PaulZC/NEO-M8T_GNSS_FeatherWing/img/PCB_BOTTOM.jpg

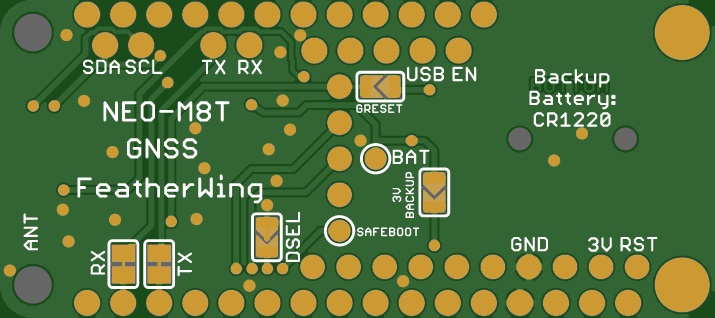
img/PCB_BOTTOM.jpg
