PaulZC/NEO-M8T_GNSS_FeatherWing/img/PCB_TOP.jpg

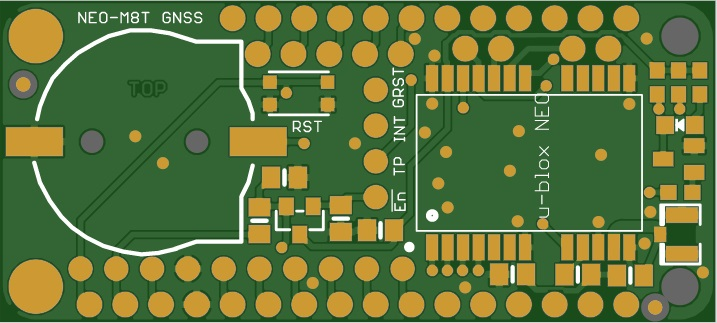
img/PCB_TOP.jpg
