PaulZC/NEO-M8T_GNSS_FeatherWing/Python/NEO-M8T_GNSS_RAWX_Logger.py

## U-Blox NEO-M8T GNSS RAWX Logger

## Hardware:
## Paul's NEO-M8T GNSS FeatherWing:
## https://github.com/PaulZC/NEO-M8T_GNSS_FeatherWing
## Mounted on the Adafruit Feather M0 Adalogger:
## https://www.adafruit.com/product/2796
## https://learn.adafruit.com/adafruit-feather-m0-adalogger

## Assumes that the Adalogger is running UBX_Echo
## https://github.com/PaulZC/NEO-M8T_GNSS_FeatherWing/tree/master/Arduino/UBX_Echo

## Logs RXM-RAWX, RXM-SFRBX and TIM-TM2 messages to file

import serial
import time
import sys
import signal
import logging

# https://stackoverflow.com/questions/842557/how-to-prevent-a-block-of-code-from-being-interrupted-by-keyboardinterrupt-in-py
class DelayedKeyboardInterrupt(object):
    def __enter__(self):
        self.signal_received = False
        self.old_handler = signal.getsignal(signal.SIGINT)
        signal.signal(signal.SIGINT, self.handler)

    def handler(self, sig, frame):
        self.signal_received = (sig, frame)
        logging.debug('SIGINT received. Delaying KeyboardInterrupt.')

    def __exit__(self, type, value, traceback):
        signal.signal(signal.SIGINT, self.old_handler)
        if self.signal_received:
            self.old_handler(*self.signal_received)

class UBXport(object):

    def __init__(self,baud=115200):
        ''' Init UBXport - open the serial port '''
        com_port = raw_input('Which serial port do you want to use (default COM1)? ')
        if com_port == '': com_port = 'COM1'

        # Open port
        try:
            self.ser1 = serial.Serial(com_port, baud, timeout=0.1)
        except:
            raise NameError('COULD NOT OPEN SERIAL PORT!')

        self.ser1.flushInput()

    def sendNMEA(self,msg,wait=10,biglen=200):
        ''' Send a message in NMEA format (adding $ and *, the checksum, and \r\n) and wait for a reply '''
        a = []
        a += "$" + msg + "*"
        csum = 0 
        for c in a[1:-1]: csum ^= ord(c)        
        a += "%02X"%csum + '\r\n'
        print 'Sending:'
        print ''.join(a[:-2])
        for c in a: self.ser1.write(c)
        if wait > 0:
            print 'Received:'
            for x in range(wait):
                RX = up.ser1.read(biglen)
                if RX != '': sys.stdout.write(RX)

    def sendUBX(self,msg,wait=10,biglen=200):
        ''' Send a message in UBX format (adding the checksum) and wait for a reply '''
        a = []
        a += msg
        sum1 = 0
        sum2 = 0
        for c in a[2:]:
            sum1 = sum1 + ord(c)
            sum2 = sum2 + sum1
        a += chr(sum1&0xFF)
        a += chr(sum2&0xFF)
        print 'Sending:'
        print "\\x" + "\\x".join("{:02x}".format(ord(c)) for c in a)
        for c in a: self.ser1.write(c)
        if wait > 0:
            print 'Received:'
            for x in range(wait):
                RX = self.ser1.read(biglen)
                if RX != '':
                    print "\\x" + "\\x".join("{:02x}".format(ord(c)) for c in RX)

rx = ''
    
try:
    print 'NEO-M8T GNSS RAWX Logger'
    print
    
    up = UBXport() # Open port

    # Disable all default NMEA messages
    print 'Disabling GLL'
    up.sendNMEA("PUBX,40,GLL,0,0,0,0")
    print 'Disabling ZDA'
    up.sendNMEA("PUBX,40,ZDA,0,0,0,0")
    print 'Disabling VTG'
    up.sendNMEA("PUBX,40,VTG,0,0,0,0")
    print 'Disabling GSV'
    up.sendNMEA("PUBX,40,GSV,0,0,0,0")
    print 'Disabling GSA'
    up.sendNMEA("PUBX,40,GSA,0,0,0,0")
    print 'Disabling RMC'
    up.sendNMEA("PUBX,40,RMC,0,0,0,0")       
    print 'Disabling GGA'
    up.sendNMEA("PUBX,40,GGA,0,0,0,0")       

    # Set Navigation Mode
    print
    print 'Setting Nav Mode'
    print '\\xb5\\x62\\x05\\x01... indicates ACK'
    print '\\xb5\\x62\\x05\\x00... indicates NACK'
    # Get Navigation Engine
    #up.sendUBX("\xB5\x62\x06\x24\x00\x00")
    # Default:   \xb5\x62\x06\x24\x24\x00\xff\xff\x02\x03\x00\x00\x00\x00\x10\x27\x00\x00\x05\x00\xfa\x00\xfa\x00\x64\x00\x5e\x01\x00\x3c\x00\x00\x00\x00\x00\x00\x03\x00\x00\x00\x00\x00
    # Set Navigation Engine dynModel to "Stationary"
    # Set tAcc to 350
    # Set dgnssTimeout to zero
    # Set utcStandard to UTC
    up.sendUBX("\xB5\x62\x06\x24\x24\x00\xFF\xFF\x02\x03\x00\x00\x00\x00\x10\x27\x00\x00\x05\x00\xFA\x00\xFA\x00\x64\x00\x5e\x01\x00\x00\x00\x00\x00\x00\x00\x00\x03\x00\x00\x00\x00\x00")
    # Set Navigation Engine dynModel to "Portable"
    #up.sendUBX("\xB5\x62\x06\x24\x24\x00\xFF\xFF\x00\x03\x00\x00\x00\x00\x10\x27\x00\x00\x05\x00\xFA\x00\xFA\x00\x64\x00\x5e\x01\x00\x00\x00\x00\x00\x00\x00\x00\x03\x00\x00\x00\x00\x00")
    # Set Navigation Engine dynModel to "Pedestrian"
    #up.sendUBX("\xB5\x62\x06\x24\x24\x00\xFF\xFF\x03\x03\x00\x00\x00\x00\x10\x27\x00\x00\x05\x00\xFA\x00\xFA\x00\x64\x00\x5e\x01\x00\x00\x00\x00\x00\x00\x00\x00\x03\x00\x00\x00\x00\x00")
    # Set Navigation Engine dynModel to "Automotive"
    #up.sendUBX("\xB5\x62\x06\x24\x24\x00\xFF\xFF\x04\x03\x00\x00\x00\x00\x10\x27\x00\x00\x05\x00\xFA\x00\xFA\x00\x64\x00\x5e\x01\x00\x00\x00\x00\x00\x00\x00\x00\x03\x00\x00\x00\x00\x00")
    # Set Navigation Engine dynModel to "Sea"
    #up.sendUBX("\xB5\x62\x06\x24\x24\x00\xFF\xFF\x05\x03\x00\x00\x00\x00\x10\x27\x00\x00\x05\x00\xFA\x00\xFA\x00\x64\x00\x5e\x01\x00\x00\x00\x00\x00\x00\x00\x00\x03\x00\x00\x00\x00\x00")
    # Set Navigation Engine dynModel to "Airborne <1G"
    #up.sendUBX("\xB5\x62\x06\x24\x24\x00\xFF\xFF\x06\x03\x00\x00\x00\x00\x10\x27\x00\x00\x05\x00\xFA\x00\xFA\x00\x64\x00\x5e\x01\x00\x00\x00\x00\x00\x00\x00\x00\x03\x00\x00\x00\x00\x00")

    # Config NMEA Talker ID
    print
    print 'Setting NMEA Config'
    # Get NMEA
    #up.sendUBX("\xb5\x62\x06\x17\x00\x00")
    # Default:   \xb5\x62\x06\x17\x14\x00\x00\x40\x00\x02\x00\x00\x00\x00\x00\x00\x00\x01\x00\x00\x00\x00\x00\x00\x00\x00
    # Set NMEA Config:
    # Set trackFilt to 1 to ensure course (COG) is always output
    # Set Main Talker ID to 'GP' to avoid having to modify TinyGPS
    up.sendUBX("\xb5\x62\x06\x17\x14\x00\x20\x40\x00\x02\x00\x00\x00\x00\x00\x01\x01\x01\x00\x00\x00\x00\x00\x00\x00\x00")
    # Set Main Talker ID to 'GN'
    #up.sendUBX("\xb5\x62\x06\x17\x14\x00\x20\x40\x00\x02\x00\x00\x00\x00\x00\x03\x01\x01\x00\x00\x00\x00\x00\x00\x00\x00")

    # Configure GNSS
    print
    print 'Configuring GNSS'
    # Get GNSS
    #up.sendUBX("\xb5\x62\x06\x3e\x00\x00")
    # Default:   \xb5\x62\x06\x3e\x3c\x00\x00\x20\x20\x07\x00\x08\x10\x00\x01\x00\x01\x01\x01\x01\x03\x00\x00\x00\x01\x01\x02\x04\x08\x00\x00\x00\x01\x01\x03\x08\x10\x00\x00\x00\x01\x01\x04\x00\x08\x00\x00\x00\x01\x03\x05\x00\x03\x00\x01\x00\x01\x05\x06\x08\x0e\x00\x01\x00\x01\x01
    # Set GNSS: GPS + QZSS + GLONASS (Default on NEO-M8T)
    #up.sendUBX("\xb5\x62\x06\x3e\x3c\x00\x00\x20\x20\x07\x00\x08\x10\x00\x01\x00\x01\x01\x01\x01\x03\x00\x00\x00\x01\x01\x02\x04\x08\x00\x00\x00\x01\x01\x03\x08\x10\x00\x00\x00\x01\x01\x04\x00\x08\x00\x00\x00\x01\x03\x05\x00\x03\x00\x01\x00\x01\x05\x06\x08\x0e\x00\x01\x00\x01\x01",30)
    # Set GNSS: GPS + Galileo + GLONASS
    #up.sendUBX("\xb5\x62\x06\x3e\x3c\x00\x00\x20\x20\x07\x00\x08\x10\x00\x01\x00\x01\x01\x01\x01\x03\x00\x00\x00\x01\x01\x02\x04\x08\x00\x01\x00\x01\x01\x03\x08\x10\x00\x00\x00\x01\x01\x04\x00\x08\x00\x00\x00\x01\x03\x05\x00\x03\x00\x00\x00\x01\x05\x06\x08\x0e\x00\x01\x00\x01\x01",30)
    # Set GNSS: GPS + Galileo + BeiDou
    #up.sendUBX("\xb5\x62\x06\x3e\x3c\x00\x00\x20\x20\x07\x00\x08\x10\x00\x01\x00\x01\x01\x01\x01\x03\x00\x00\x00\x01\x01\x02\x04\x08\x00\x01\x00\x01\x01\x03\x08\x10\x00\x01\x00\x01\x01\x04\x00\x08\x00\x00\x00\x01\x03\x05\x00\x03\x00\x00\x00\x01\x05\x06\x08\x0e\x00\x00\x00\x01\x01",30)
    # Set GNSS: GPS + Galileo + GLONASS + SBAS
    up.sendUBX("\xb5\x62\x06\x3e\x3c\x00\x00\x20\x20\x07\x00\x08\x10\x00\x01\x00\x01\x01\x01\x01\x03\x00\x01\x00\x01\x01\x02\x04\x08\x00\x01\x00\x01\x01\x03\x08\x10\x00\x00\x00\x01\x01\x04\x00\x08\x00\x00\x00\x01\x03\x05\x00\x03\x00\x00\x00\x01\x05\x06\x08\x0e\x00\x01\x00\x01\x01",30)
    # Set GNSS: GPS + Galileo + BeiDou + SBAS
    #up.sendUBX("\xb5\x62\x06\x3e\x3c\x00\x00\x20\x20\x07\x00\x08\x10\x00\x01\x00\x01\x01\x01\x01\x03\x00\x01\x00\x01\x01\x02\x04\x08\x00\x01\x00\x01\x01\x03\x08\x10\x00\x01\x00\x01\x01\x04\x00\x08\x00\x00\x00\x01\x03\x05\x00\x03\x00\x00\x00\x01\x05\x06\x08\x0e\x00\x00\x00\x01\x01",30)

    # Change Navigation/Measurement Rate
    print
    print 'Setting Measurement Rate'
    # Get CFG-RATE
    #up.sendUBX("\xb5\x62\x06\x08\x00\x00")
    # Default:   \xb5\x62\x06\x08\x06\x00\xe8\x03\x01\x00\x01\x00
    # Set CFG-RATE: set measRate to 250msec; align to UTC time
    up.sendUBX("\xb5\x62\x06\x08\x06\x00\xfa\x00\x01\x00\x00\x00")
    # Set CFG-RATE: set measRate to 250msec; align to GPS time
    #up.sendUBX("\xb5\x62\x06\x08\x06\x00\xfa\x00\x01\x00\x01\x00")
    # Set CFG-RATE: set measRate to 500msec; align to UTC time
    #up.sendUBX("\xb5\x62\x06\x08\x06\x00\xf4\x01\x01\x00\x00\x00")
    # Set CFG-RATE: set measRate to 1000msec; align to UTC time
    #up.sendUBX("\xb5\x62\x06\x08\x06\x00\xe8\x03\x01\x00\x00\x00")
    # Set CFG-RATE: set measRate to 10000msec; align to UTC time
    #up.sendUBX("\xb5\x62\x06\x08\x06\x00\x10\x27\x01\x00\x00\x00")

    # Send the next two messages without waiting for an acknowledgement

    # Set RXM-RAWX message rate (once per measRate)
    print
    print 'Setting RXM-RAWX Message Rate'
    # Poll RXM-RAWX send rate
    #up.sendUBX("\xb5\x62\x06\x01\x02\x00\x02\x15")
    # Default:   \xb5\x62\x06\x01\x08\x00\x02\x15\x00\x00\x00\x00\x00\x00
    # Set RXM-RAWX send rate
    up.sendUBX("\xb5\x62\x06\x01\x03\x00\x02\x15\x01",0) # current port
    #up.sendUBX("\xb5\x62\x06\x01\x08\x00\x02\x15\x00\x01\x00\x00\x00\x00",0) # six ports
    # Disable RXM-RAWX messages
    #up.sendUBX("\xb5\x62\x06\x01\x03\x00\x02\x15\x00",0) # current port

    # Set RXM-SFRBX message rate (once per measRate)
    print
    print 'Setting RXM-SFRBX Message Rate'
    # Poll RXM-SFRBX send rate
    #up.sendUBX("\xb5\x62\x06\x01\x02\x00\x02\x13")
    # Default:   \xb5\x62\x06\x01\x08\x00\x02\x13\x00\x00\x00\x00\x00\x00
    # Set RXM-SFRBX send rate
    up.sendUBX("\xb5\x62\x06\x01\x03\x00\x02\x13\x01",0) # current port
    #up.sendUBX("\xb5\x62\x06\x01\x08\x00\x02\x13\x00\x01\x00\x00\x00\x00",0) # six ports
    # Disable RXM-SFRBX messages
    #up.sendUBX("\xb5\x62\x06\x01\x03\x00\x02\x13\x00",0) # current port

    # Use this message to mop up the acknowledgements for all three

    # Set TIM-TM2 message rate (once per measRate)
    print
    print 'Setting TIM-TM2 Message Rate'
    # Poll TIM-TM2 send rate
    #up.sendUBX("\xb5\x62\x06\x01\x02\x00\x0d\x03")
    # Default:   \xb5\x62\x06\x01\x08\x00\x0d\x03\x00\x00\x00\x00\x00\x00
    # Set TIM-TM2 send rate
    up.sendUBX("\xb5\x62\x06\x01\x03\x00\x0d\x03\x01",1,30) # current port
    #up.sendUBX("\xb5\x62\x06\x01\x08\x00\x0d\x03\x00\x01\x00\x00\x00\x00",1,30) # six ports
    # Disable TIM-TM2 messages
    #up.sendUBX("\xb5\x62\x06\x01\x03\x00\x0d\x03\x00",1,30) # current port

    start_time = time.time() # Get the time
    tn = time.localtime(start_time) # Extract the time and date as strings
    date_str = str(tn[0])+str(tn[1]).zfill(2)+str(tn[2]).zfill(2)
    time_str = str(tn[3]).zfill(2)+str(tn[4]).zfill(2)+str(tn[5]).zfill(2)
    # Assemble the file name using the date, time and port name
    filename = 'GNSS_RAWX_Log_' + date_str + '_' + time_str + '.bin'
    print
    print 'Logging data to', filename
    print
    print 'Press CTRL+C to stop logging'
    print

    fp = open(filename, 'wb') # Create / clear the file

    while True:
        # We don't want KeyboardInterrupt to interrupt this!
        with DelayedKeyboardInterrupt():
            rx = up.ser1.read(200) # Read serial data forcing a timeout if required
            if rx != '': # if we got some data:
                # write it to the file
                fp.write(rx)
                # print it in Python hex syntax (useful for cutting and pasting)
                rx_str = "\\x" + "\\x".join("{:02x}".format(ord(c)) for c in rx)
                sys.stdout.write(rx_str)
        # Let KeyboardInterrupt interrupt now
        pass

except KeyboardInterrupt:
    print
    print 'CTRL+C received...'
    print
    print 'Disabling messages...'
    up.sendUBX("\xb5\x62\x06\x01\x03\x00\x02\x15\x00",0) # Disable RXM-RAWX
    up.sendUBX("\xb5\x62\x06\x01\x03\x00\x02\x13\x00",0) # Disable RXM-SFRBX
    up.sendUBX("\xb5\x62\x06\x01\x03\x00\x0d\x03\x00",0) # Disable TIM-TM2

    # Wait ~1sec for any remaining data to arrive and write it to disk
    # Leave 30 bytes in the receive buffer as these should be the
    # three x 10 byte acknowledgements from the disable messages
    nodata = 0
    while nodata < 1000:
        buflen = up.ser1.inWaiting() # See if there is any data left to be read
        if buflen > 30: # if there is data left to be read
            rx = up.ser1.read(buflen - 30) # read the data
            # print it in Python hex syntax (useful for cutting and pasting)
            rx_str = "\\x" + "\\x".join("{:02x}".format(ord(c)) for c in rx)
            sys.stdout.write(rx_str)
            # and write it to the file
            fp.write(rx)
        else: # there are 0 - 30 bytes waiting
            time.sleep(0.001)
            nodata += 1
    print
    print "Final receive buffer length should be 30. It was %i."%buflen
    if buflen > 0:
        # Print the remaining data without writing it to file
        rx = up.ser1.read(buflen) # read the data
        # print it in Python hex syntax (useful for cutting and pasting)
        rx_str = "\\x" + "\\x".join("{:02x}".format(ord(c)) for c in rx)
        sys.stdout.write(rx_str)
           
finally:
    up.ser1.close() # Close the serial port
    fp.close() # Close the file
    print
    print 'Bye!'
